tompaton/grandpa-amus-bridge/photos/20200714_222248.jpg

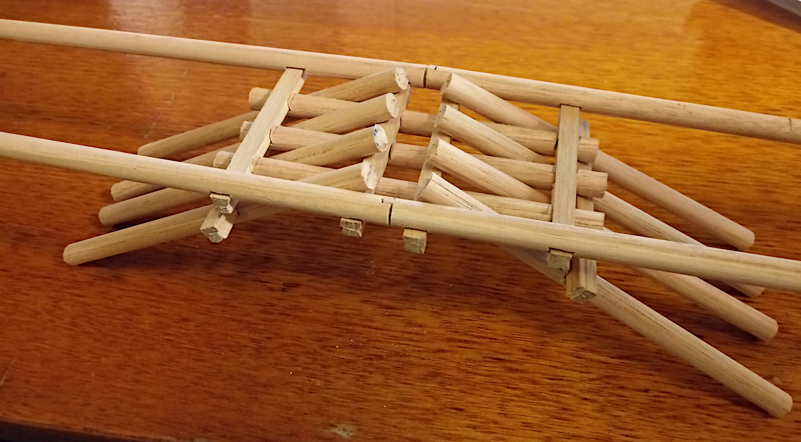
photos/20200714_222248.jpg
